brainsmoke/desklamp/firmware/attiny1624/gamma.c

#include <stdint.h>

#include "config.h"

#define GAMMA_MIN (10)
#define GAMMA_DEFAULT (20)
#define GAMMA_MAX (55)

/* N tables with 33 entries packed into N*32+1 entries, next table's 0 doubles as 0x10000 */
/* so don't change the type from uint16_t */

static const uint16_t gamma_table[ (1+GAMMA_MAX-GAMMA_MIN)*32 + 1] =
{
/*
for i in range(10,55+1):
    g = i/10
    f = 65536/(32**g)
    print ('\t'+', '.join(str(int(.5+f*x**g)) for x in range(32)) + ',')
print("\t0")
*/
	0, 2048, 4096, 6144, 8192, 10240, 12288, 14336, 16384, 18432, 20480, 22528, 24576, 26624, 28672, 30720, 32768, 34816, 36864, 38912, 40960, 43008, 45056, 47104, 49152, 51200, 53248, 55296, 57344, 59392, 61440, 63488,
	0, 1448, 3104, 4849, 6654, 8505, 10394, 12315, 14263, 16236, 18231, 20246, 22280, 24331, 26397, 28478, 30574, 32682, 34803, 36935, 39079, 41234, 43399, 45574, 47758, 49952, 52154, 54364, 56583, 58810, 61045, 63287,
	0, 1024, 2353, 3827, 5405, 7064, 8792, 10578, 12417, 14302, 16229, 18196, 20198, 22235, 24303, 26400, 28526, 30679, 32857, 35059, 37285, 39533, 41803, 44093, 46404, 48734, 51082, 53449, 55833, 58234, 60652, 63086,
	0, 724, 1783, 3020, 4390, 5867, 7437, 9087, 10809, 12598, 14447, 16353, 18311, 20319, 22374, 24474, 26616, 28798, 31020, 33279, 35573, 37903, 40266, 42661, 45088, 47545, 50032, 52548, 55092, 57664, 60262, 62886,
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
{
	if (gamma_dec < GAMMA_MIN)
		gamma_dec = GAMMA_MIN;

	else if (gamma_dec > GAMMA_MAX)
		gamma_dec = GAMMA_MAX;

	gamma = gamma_dec;
	cur_table = &gamma_table[ (gamma_dec - GAMMA_MIN) * 32 ];
}

uint8_t gamma_get(void)
{
	return gamma;
}

void gamma_set_max(uint16_t max)
{
	limit = (uint32_t)max+1; /* ((max+1)*0xffff)>>16 is max */
}

uint16_t gamma_get_max(void)
{
	return limit-1;
}

uint16_t gamma_translate(uint16_t v)
{
	uint8_t ix = v>>11;
	uint16_t diff = cur_table[ix+1] - cur_table[ix]; /* make use of integer wraparound if ix == 32 */
	uint32_t res = v&0x7ff;

	res *= diff;
	res >>= 11;
	res += cur_table[ix];
	res *= limit;
	return res >> 16;
}
