brainsmoke/desklamp/firmware/attiny1624/prot.c

#include <ctype.h>
#include <stdlib.h>
#include <string.h>

#include "config.h"

#include "prot.h"
#include "uart.h"
#include "dial.h"
#include "settings.h"
#include "system.h"
#include "gamma.h"
#include "io.h"
#include "firmware.h"
#include "ani.h"

enum
{
	CMD_BLINK,
	CMD_DEBUG,
	CMD_FACTORY_RESET,
	CMD_HELP,
	CMD_LOAD_CALIB,
	CMD_LOAD_PRESET,
	CMD_OFF,
	CMD_ON,
	CMD_PRINT,
	CMD_RESET,
	CMD_RESTORE_CALIB,
	CMD_RESTORE_PRESET,
	CMD_SAVE_CALIB,
	CMD_SAVE_PRESET,
	CMD_SET_GAMMA,
	CMD_SET_LED,
	CMD_SET_LEDS,
	CMD_SET_MAX_BRIGHTNESS,
	CMD_UNKNOWN_COMMAND,
	CMD_SYNTAX_ERROR,
};

typedef struct
{

	const char *name;
	uint8_t len;

	uint8_t cmd;

	const char *arglist;

} cmd_t;

static const cmd_t commands[] =
{
	#define C(str, command, alist) { .name = str, .cmd = command, .len = sizeof(str)-1, .arglist = alist }
	/* commands are assumed to be in alphabetical order:    */
	C( "blink",                 CMD_BLINK,               ""    ),
	C( "debug",                 CMD_DEBUG,               ""    ),
	C( "factory reset",         CMD_FACTORY_RESET,       ""    ),
	C( "help",                  CMD_HELP,                ""    ),
	C( "load blink",            CMD_LOAD_PRESET,         "bF"  ),
	C( "load calibrations",     CMD_LOAD_CALIB,          ""    ),
	C( "load custom",           CMD_LOAD_PRESET,         "cF"  ),
	C( "load default",          CMD_LOAD_PRESET,         "dF"  ),
	C( "off",                   CMD_OFF,                 "F"   ),
	C( "on",                    CMD_ON,                  "F"   ),
	C( "print",                 CMD_PRINT,               ""    ),
	C( "reset",                 CMD_RESET,               ""    ),
	C( "restore blink",         CMD_RESTORE_PRESET,      "b"   ),
	C( "restore calibrations",  CMD_RESTORE_CALIB,       ""    ),
	C( "restore custom",        CMD_RESTORE_PRESET,      "c"   ),
	C( "restore default",       CMD_RESTORE_PRESET,      "d"   ),
	C( "save blink",            CMD_SAVE_PRESET,         "b"   ),
	C( "save calibrations",     CMD_SAVE_CALIB,          ""    ),
	C( "save custom",           CMD_SAVE_PRESET,         "c"   ),
	C( "save default",          CMD_SAVE_PRESET,         "d"   ),
	C( "set gamma",             CMD_SET_GAMMA,           "G"   ),
	C( "set led",               CMD_SET_LED,             "lLF" ),
	C( "set leds",              CMD_SET_LEDS,            "CF"  ),
	C( "set max brightness",    CMD_SET_MAX_BRIGHTNESS,  "B"   ),
	#undef C
};

#define N_COMMANDS (sizeof(commands)/sizeof(commands[0]) )

static const struct
{
	char x;
	const char *desc;
} args_help[] =
{
	{ 'l', " " STR_LED_RANGE },
	{ 'c', " " STR_CUSTOM_RANGE },
	{ 'b', "" },
	{ 'd', "" },
	{ 'B', " " STR_BRIGHTNESS_RANGE },
	{ 'L', " (" STR_BRIGHTNESS_RANGE " | " STR_DIAL_RANGE "[:" STR_BRIGHTNESS_RANGE "])" },
	{ 'C', " (" STR_BRIGHTNESS_RANGE " | " STR_DIAL_RANGE "[:" STR_BRIGHTNESS_RANGE "]) x " STR_N_LEDS },
	{ 'G', " " STR_GAMMA_RANGE },
	{ 'F', " [fade " STR_FADE_RANGE"]" },
	{ '\0', "" },
};

const char *get_arg_help(char x)
{
	uint8_t i;
	for (i=0; args_help[i].x; i++)
		if (args_help[i].x == x)
			return args_help[i].desc;

	return "<error>";
}

static struct
{
	uint16_t led;
	uint16_t preset;
	uint16_t timeout;
	uint16_t n;
	ledconfig_t config;
	uint8_t gamma;
	uint8_t dial;

} args;

void help(void)
{
	println("commands:");
	println("");

	const cmd_t *cmd;
	for (cmd=&commands[0]; cmd->name; cmd++)
	{
		print(cmd->name);
		const char *a;
		for (a=cmd->arglist ; *a; a++)
			print(get_arg_help(*a));

		println("");
	}
	println("");
}

static uint8_t parse_args(uint8_t *s, const char *a)
{
	args.timeout = DEFAULT_FADE;

	for (; *a; a++)
	{
		switch (*a)
		{
			case 'd':
				args.preset = PRESET_DEFAULT;
				continue;
			case 'b':
				args.preset = PRESET_BLINK;
				continue;
		}

		if ( (*s != ' ') && (*s != '\0') )
			return 0;

		while (*s == ' ')
			s++;

		switch (*a)
		{
			case 'B':
				s = parse_brightness(s, &args.n);
				break;
			case 'l':
				s = parse_u16(s, &args.led);
				if (args.led >= N_LEDS)
					s=NULL;
				break;
			case 'c':
				s = parse_u16(s, &args.preset);
				if (args.preset >= N_CUSTOM)
					s=NULL;
				args.preset += PRESET_CUSTOM_BASE;
				break;
			case 'L':
				s = parse_single_led_config(s, &args.dial, &args.n);
				break;
			case 'G':
				s = parse_u8_one_decimal(s, &args.gamma);
				break;
			case 'F':
				if (*s)
					s = parse_fade(s, &args.timeout, FADE_MAX);
				break;
			case 'C':
				s = parse_led_config(s, &args.config);
				break;
		}

		if (!s)
			return 0;
	}

	while (*s == ' ')
		s++;

	return ( *s == '\0' || *s == '#' );
}

#define CMD_MAX (128)
static uint8_t line[CMD_MAX+1];

static void process_cmd(uint8_t *cmd_line)
{
	int8_t i;
	uint8_t cmd=CMD_UNKNOWN_COMMAND;
	uint8_t *s=NULL;

	for (i=N_COMMANDS-1; i>=0; i--)
	{
		int res = strncasecmp((char *)cmd_line, commands[i].name, commands[i].len);
		if (res < 0)
//		if (res != 0)
			continue;
		else if (res > 0)
			break;

		s = &cmd_line[commands[i].len];
		if (*s != '\0' && *s != ' ')
			continue;

		cmd = commands[i].cmd;

		if (!parse_args(s, commands[i].arglist))
			cmd = CMD_SYNTAX_ERROR;

		break;
	}

	switch (cmd)
	{
		case CMD_BLINK:
			ani_blink();
			break;
		case CMD_DEBUG:
			debug_print();
			break;
		case CMD_FACTORY_RESET:
			println ("factory reset");
			factory_reset();
			break;
		case CMD_HELP:
			help();
			break;
		case CMD_LOAD_CALIB:
			println ("loading eeprom");
			load();
			break;
		case CMD_LOAD_PRESET:
			read_preset(args.preset, &args.config);
			ani_add(&args.config, args.timeout);
			break;
		case CMD_RESET:
			println ("resetting");
			flush();
			reset();
			break;
		case CMD_RESTORE_CALIB:
			restore();
			load();
			break;
		case CMD_RESTORE_PRESET:
			write_preset(args.preset, &preset_restore[args.preset]);
			if (args.preset == PRESET_DEFAULT)
				ani_add(&preset_restore[args.preset], args.timeout);
			break;
		case CMD_SAVE_CALIB:
			println ("saving eeprom");
			save();
			break;
		case CMD_SAVE_PRESET:
			ani_get_frame_top(&args.config);
			write_preset(args.preset, &args.config);
			break;
		case CMD_SET_GAMMA:
			gamma_set(args.gamma);
			print ("gamma: ");
			print_u32_fixed_point(gamma_get(), 1);
			println ("");
			break;
		case CMD_SET_LED:
			ani_get_frame_top(&args.config);
			args.config.dial[args.led] = args.dial;
			args.config.brightness[args.led] = args.n;
			ani_add(&args.config, args.timeout);
			break;
		case CMD_SET_LEDS:
			ani_add(&args.config, args.timeout);
			break;
		case CMD_SET_MAX_BRIGHTNESS:
			gamma_set_max(args.n);
			print ("max brightness: ");
			print_brightness(gamma_get_max());
			println ("");
			break;
		case CMD_PRINT:
			print_state();
			break;
		case CMD_OFF:
			ani_off(args.timeout);
			break;
		case CMD_ON:
			ani_on(args.timeout);
			break;
		case CMD_UNKNOWN_COMMAND:
			println ("unknown command");
			break;
		case CMD_SYNTAX_ERROR:
			println ("syntax error");
			break;
		default:
			println ("internal error");
			break;
	}
}

static void write_prompt(void)
{
	print("lampsh> ");
}

void prot_poll(void)
{
	static uint16_t ix=0;
	static uint8_t last = 0;
	int c;
	while ( (c = uart_getchar()) != -1)
	{
		if (c == '\t')
			c = ' ';

		if ( (c == '\n') && (last == '\r') )
			continue;

		if ( (c == '\r') || (c == '\n') )
		{
			println("");
			line[ix] = '\0';
			if (ix > 0)
				process_cmd(line);
			write_prompt();
			ix = 0;
		}
		else if (isprint(c) && !(last == ' ' && c == ' '))
		{
			uart_putchar(c);

			if (ix < CMD_MAX)
				line[ix++] = c;
		}
		else if ( (c == '\b' || c == '\x7f') && ix > 0)
		{
			ix--;
			print("\b \b");
		}

		last = c;
	}
}

void prot_init(void)
{
	println("");
	println ("I am a lamp");
	write_prompt();
}
